consp/lcd8-re/src/hal/lcd8h/at32f435/cntl.c

#include "controls.h"
#include "comm.h"
#include "delay.h"
#include "lcd.h"
#include "at32f435_437.h"
#include "hal/lcd8/at32f435/cntl.h"

#include "config.h"
#include "eeprom.h"
#include "gui.h"

extern settings_t settings;

const int NTC_table[1025] = {
  105972, 90128, 74284, 66383, 61277, 57570, 
  54690, 52352, 50395, 48718, 47256, 45963, 
  44806, 43760, 42808, 41936, 41131, 40384, 
  39689, 39038, 38428, 37853, 37310, 36795, 
  36307, 35842, 35399, 34976, 34571, 34182, 
  33810, 33451, 33106, 32774, 32453, 32143, 
  31843, 31553, 31272, 30999, 30734, 30477, 
  30228, 29985, 29748, 29518, 29294, 29075, 
  28861, 28653, 28449, 28250, 28056, 27865, 
  27679, 27497, 27319, 27144, 26972, 26804, 
  26639, 26478, 26319, 26163, 26010, 25860, 
  25712, 25567, 25424, 25283, 25145, 25009, 
  24875, 24744, 24614, 24486, 24360, 24236, 
  24114, 23993, 23875, 23757, 23642, 23528, 
  23415, 23304, 23195, 23087, 22980, 22874, 
  22770, 22667, 22566, 22465, 22366, 22268, 
  22171, 22075, 21980, 21887, 21794, 21702, 
  21611, 21522, 21433, 21345, 21258, 21172, 
  21087, 21002, 20919, 20836, 20754, 20673, 
  20593, 20513, 20434, 20356, 20279, 20202, 
  20126, 20051, 19976, 19902, 19828, 19756, 
  19683, 19612, 19541, 19471, 19401, 19331, 
  19263, 19195, 19127, 19060, 18993, 18927, 
  18862, 18797, 18732, 18668, 18605, 18541, 
  18479, 18416, 18355, 18293, 18232, 18172, 
  18112, 18052, 17993, 17934, 17876, 17818, 
  17760, 17703, 17646, 17589, 17533, 17477, 
  17421, 17366, 17311, 17257, 17203, 17149, 
  17096, 17042, 16990, 16937, 16885, 16833, 
  16781, 16730, 16679, 16628, 16578, 16527, 
  16478, 16428, 16379, 16329, 16281, 16232, 
  16184, 16136, 16088, 16040, 15993, 15946, 
  15899, 15853, 15806, 15760, 15714, 15669, 
  15623, 15578, 15533, 15488, 15444, 15399, 
  15355, 15311, 15268, 15224, 15181, 15138, 
  15095, 15052, 15009, 14967, 14925, 14883, 
  14841, 14800, 14758, 14717, 14676, 14635, 
  14594, 14554, 14513, 14473, 14433, 14393, 
  14354, 14314, 14275, 14235, 14196, 14157, 
  14119, 14080, 14041, 14003, 13965, 13927, 
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
};
 
extern adc_data_t adc;
extern volatile uint32_t timer_counter;

extern uint8_t power_button_state ;
extern uint8_t up_button_state ;
extern uint8_t down_button_state ;
extern uint8_t nc_button_state ;
extern uint8_t light_state ;

extern uint32_t power_button_start;
extern uint32_t up_button_start;
extern uint32_t down_button_start;
extern uint32_t nc_button_start;
extern uint32_t button_backoff, button_backoff_start;

int32_t ext_temp_store = 0; // store temperature adc value in case button is pressed

/**
 * static functions
 */
static void adc_config(void) {
    adc_base_config_type adc_base_struct;
    crm_periph_clock_enable(CRM_ADC1_PERIPH_CLOCK, TRUE); // use default perph clock
    /* crm_adc_clock_div_set(CRM_ADC_DIV_6); // */

    adc_common_config_type adc_common_struct;
    adc_common_default_para_init(&adc_common_struct);
    adc_common_struct.combine_mode = ADC_INDEPENDENT_MODE;
    adc_common_struct.div = ADC_HCLK_DIV_4;
    adc_common_struct.common_dma_mode = ADC_COMMON_DMAMODE_DISABLE;
    adc_common_struct.common_dma_request_repeat_state = FALSE;
    adc_common_struct.sampling_interval = ADC_SAMPLING_INTERVAL_5CYCLES;
    adc_common_struct.tempervintrv_state = FALSE;
    adc_common_struct.vbat_state = FALSE;
    adc_common_config(&adc_common_struct);

    adc_base_default_para_init(&adc_base_struct);
    adc_base_struct.sequence_mode = TRUE;
    adc_base_struct.repeat_mode = FALSE;
    adc_base_struct.data_align = ADC_RIGHT_ALIGNMENT;
    adc_base_struct.ordinary_channel_length = 6;
    adc_base_config(ADC1, &adc_base_struct);
    adc_resolution_set(ADC1, ADC_RESOLUTION_12B);
    adc_ordinary_channel_set(ADC1, ADC_CHANNEL_16, 1, ADC_SAMPLETIME_247_5);
    adc_ordinary_channel_set(ADC1, ADC_CHANNEL_17, 2, ADC_SAMPLETIME_247_5);
    adc_ordinary_channel_set(ADC1, VOLTAGE_DETECT_ADC_CH, 3, ADC_SAMPLETIME_247_5);
    adc_ordinary_channel_set(ADC1, EXT_TEMP_ADC_CH, 4, ADC_SAMPLETIME_247_5);
    adc_ordinary_channel_set(ADC1, NC_BUTTON_ADC_CH, 5, ADC_SAMPLETIME_247_5);
    adc_ordinary_channel_set(ADC1, POWER_BUTTON_ADC_CH, 6, ADC_SAMPLETIME_247_5);

    adc_dma_request_repeat_enable(ADC1, TRUE);
    adc_ordinary_conversion_trigger_set(ADC1, ADC_ORDINARY_TRIG_TMR1CH1, ADC_ORDINARY_TRIG_EDGE_NONE);
    adc_ordinary_software_trigger_enable(ADC1, TRUE);
    /* adc_ordinary_conversion_trigger_set(ADC1, ADC123_ORDINARY_TRIG_SOFTWARE, TRUE); */

    adc_dma_mode_enable(ADC1, TRUE);
    /* adc_tempersensor_vintrv_enable(TRUE); // required only for temp sensor */

    adc_enable(ADC1, TRUE);
    adc_calibration_init(ADC1);
    while(adc_calibration_init_status_get(ADC1));
    adc_calibration_start(ADC1);
    while(adc_calibration_status_get(ADC1));
}

static void dma_config(void)
{
    dma_init_type dma_init_struct;
    crm_periph_clock_enable(CRM_DMA1_PERIPH_CLOCK, TRUE);
    dma_reset(DMA1_CHANNEL1);
    dma_default_para_init(&dma_init_struct);
    dma_init_struct.buffer_size = 6;
    dma_init_struct.direction = DMA_DIR_PERIPHERAL_TO_MEMORY;
    dma_init_struct.memory_base_addr = (uint32_t) &adc;
    dma_init_struct.memory_data_width = DMA_MEMORY_DATA_WIDTH_HALFWORD;
    dma_init_struct.memory_inc_enable = TRUE;
    dma_init_struct.peripheral_base_addr = (uint32_t)&(ADC1->odt);
    dma_init_struct.peripheral_data_width = DMA_PERIPHERAL_DATA_WIDTH_HALFWORD;
    dma_init_struct.peripheral_inc_enable = FALSE;
    dma_init_struct.priority = DMA_PRIORITY_HIGH;
    dma_init_struct.loop_mode_enable = TRUE;
    dma_init(DMA1_CHANNEL1, &dma_init_struct);

    dmamux_enable(DMA1, TRUE);
    dmamux_init(DMA1MUX_CHANNEL1, DMAMUX_DMAREQ_ID_ADC1);

    dma_channel_enable(DMA1_CHANNEL1, TRUE);
}

static void tmr_config(void) {

    crm_periph_clock_enable(CRM_TMR14_PERIPH_CLOCK, TRUE);
    /* tmr_output_config_type tmr_oc_init_structure; */
    /* tmre base configuration */
    tmr_base_init(TMR14,  BUTTON_MEASURE_PERIOD * 1000, TIMER_FREQ(1000000));
    /* tmr_base_init(TMR14,  BUTTON_MEASURE_PERIOD * 1000, 1000000); */
    tmr_cnt_dir_set(TMR14, TMR_COUNT_UP);
    tmr_clock_source_div_set(TMR14, TMR_CLOCK_DIV1);

    /* output compare toggle mode configuration: channel1 */
    /* tmr_output_default_para_init(&tmr_oc_init_structure); */
    /* tmr_oc_init_structure.oc_mode = TMR_OUTPUT_CONTROL_SWITCH; */
    /* tmr_oc_init_structure.oc_idle_state = FALSE; */
    /* tmr_oc_init_structure.oc_polarity = TMR_OUTPUT_ACTIVE_LOW; */
    /* tmr_oc_init_structure.oc_output_state = FALSE; */
    /* tmr_output_channel_config(TMR14, TMR_SELECT_CHANNEL_1, &tmr_oc_init_structure); */
    /* tmr_channel_value_set(TMR14, TMR_SELECT_CHANNEL_1, 1000); */
    tmr_counter_enable(TMR14, TRUE);
    tmr_interrupt_enable(TMR14, TMR_OVF_INT, TRUE);
    
    nvic_priority_group_config(NVIC_PRIORITY_GROUP_4);
    nvic_irq_enable(TMR8_TRG_HALL_TMR14_IRQn, 0, 0);
}

/**
 * public functions
 */

void controls_init(void) {
    // enable clocks
    crm_periph_clock_enable(CRM_GPIOA_PERIPH_CLOCK, TRUE);
    // configure pins
    //
    gpio_init_type gpio_initstructure;

    gpio_initstructure.gpio_out_type       = GPIO_OUTPUT_PUSH_PULL; // input
    gpio_initstructure.gpio_pull           = POWER_BUTTON_PULL; // external pullup
    gpio_initstructure.gpio_mode           = POWER_BUTTON_MODE;
    gpio_initstructure.gpio_drive_strength = GPIO_DRIVE_STRENGTH_STRONGER; // input
    gpio_initstructure.gpio_pins           = POWER_BUTTON_PIN;
    gpio_init(POWER_BUTTON_GPIO, &gpio_initstructure);

    gpio_initstructure.gpio_out_type       = GPIO_OUTPUT_PUSH_PULL; // input
    gpio_initstructure.gpio_pull           = UP_BUTTON_PULL; // external pullup
    gpio_initstructure.gpio_mode           = UP_BUTTON_MODE;
    gpio_initstructure.gpio_drive_strength = GPIO_DRIVE_STRENGTH_STRONGER; // input
    gpio_initstructure.gpio_pins           = UP_BUTTON_PIN;
    gpio_init(UP_BUTTON_GPIO, &gpio_initstructure);

    gpio_initstructure.gpio_out_type       = GPIO_OUTPUT_PUSH_PULL; // input
    gpio_initstructure.gpio_pull           = DOWN_BUTTON_PULL; // external pullup
    gpio_initstructure.gpio_mode           = DOWN_BUTTON_MODE;
    gpio_initstructure.gpio_drive_strength = GPIO_DRIVE_STRENGTH_STRONGER; // input
    gpio_initstructure.gpio_pins           = DOWN_BUTTON_PIN;
    gpio_init(DOWN_BUTTON_GPIO, &gpio_initstructure);

    gpio_initstructure.gpio_out_type       = GPIO_OUTPUT_PUSH_PULL; // input
    gpio_initstructure.gpio_pull           = POWER_LATCH_PULL; // external pullup
    gpio_initstructure.gpio_mode           = POWER_LATCH_MODE;
    gpio_initstructure.gpio_drive_strength = GPIO_DRIVE_STRENGTH_STRONGER; // input
    gpio_initstructure.gpio_pins           = POWER_LATCH_PIN;
    gpio_init(POWER_LATCH_GPIO, &gpio_initstructure);

    gpio_initstructure.gpio_out_type       = GPIO_OUTPUT_PUSH_PULL; // input
    gpio_initstructure.gpio_pull           = VOLTAGE_DETECT_PULL; // external pullup
    gpio_initstructure.gpio_mode           = VOLTAGE_DETECT_MODE;
    gpio_initstructure.gpio_drive_strength = GPIO_DRIVE_STRENGTH_STRONGER; // input
    gpio_initstructure.gpio_pins           = VOLTAGE_DETECT_PIN;
    gpio_init(VOLTAGE_DETECT_GPIO, &gpio_initstructure);

    gpio_initstructure.gpio_out_type       = GPIO_OUTPUT_PUSH_PULL; // input
    gpio_initstructure.gpio_pull           = NC_BUTTON_PULL; // external pullup
    gpio_initstructure.gpio_mode           = NC_BUTTON_MODE;
    gpio_initstructure.gpio_drive_strength = GPIO_DRIVE_STRENGTH_STRONGER; // input
    gpio_initstructure.gpio_pins           = NC_BUTTON_PIN;
    gpio_init(NC_BUTTON_GPIO, &gpio_initstructure);

#ifdef LEXT_INSTALLED
    /* gpio_initstructure.gpio_out_type       = GPIO_OUTPUT_PUSH_PULL; // input */
    /* gpio_initstructure.gpio_pull           = GPIO_PULL_NONE; // external pullup */
    /* gpio_initstructure.gpio_mode           = GPIO_MODE_MUX; */
    /* gpio_initstructure.gpio_drive_strength = GPIO_DRIVE_STRENGTH_STRONGER; // input */
    /* gpio_initstructure.gpio_pins           = GPIO_PINS_3; */
    /* gpio_init(VOLTAGE_DETECT_GPIO, &gpio_initstructure); */
#endif

    // configure ADC
    //
    dma_config();
    adc_config();
    tmr_config();

}

CRITICAL void power_enable(void) { POWER_LATCH_GPIO->scr = POWER_LATCH_PIN; }
CRITICAL void power_disable(void) { 
    lcd_backlight(0); // "show off"
#if UART_COMM == UART_COMM_VESC
    comm_vesc_packet_send_shutdown();
#endif
    int n = 0;
    while(n < 100) {
#ifndef DEBUG
        wdt_counter_reload();
#endif
        delay_ms(25);
        n++;
    }
    // cap should keep it fed for a while
    POWER_LATCH_GPIO->clr = POWER_LATCH_PIN; 
#if LEXT_INSTALLED
    // keep alive on batt power
    // if not backup batt installed brownout will happen
    /* EXINT->inten |= EXINT_LINE_6; */
    /* pwc_voltage_regulate_set(PWC_REGULATOR_LOW_POWER); // does almost nothing */
    /* pwc_deep_sleep_mode_enter(PWC_DEEP_SLEEP_ENTER_WFI);  */
    // goes to deepsleep, power consumption in deepsleep and standby is the same (mostly leakage anyway)
    // recover on interrupt

    /* wait clock stable */
    /* for(int index = 0; index < 300; index++) */
    /* { */
    /*   __NOP(); */
    /* } */
    /* pwc_voltage_regulate_set(PWC_REGULATOR_ON); */
    /*  */
    /* // reset */
    /* NVIC_SystemReset(); */
#endif
}

volatile uint32_t xun = 0;
static inline int power_button_measure(void) {
    if (POWER_BUTTON_MODE == GPIO_MODE_INPUT) return (POWER_BUTTON_GPIO->idt & (POWER_BUTTON_PIN)) > 0;
    return adc.power_button >= 3*1024;
}

static inline int down_button_measure(void) {
    if (DOWN_BUTTON_MODE == GPIO_MODE_INPUT) return (DOWN_BUTTON_GPIO->idt & (DOWN_BUTTON_PIN)) == 0;
    return adc.down_button <= 10;
}

static inline int up_button_measure(void) {
    if (UP_BUTTON_MODE == GPIO_MODE_INPUT) return (UP_BUTTON_GPIO->idt & (UP_BUTTON_PIN)) == 0;
    return adc.up_button <= 10;
}

static inline int nc_button_measure(void) {
    if (NC_BUTTON_MODE == GPIO_MODE_INPUT) return (NC_BUTTON_GPIO->idt & (NC_BUTTON_PIN)) > 0;
    return adc.nc_button <= 10;
}

int32_t int_temp(void) {
    // data from artery example code converted to return 24.8s fixed point format
#define ADC_TEMP_BASE                    ((int32_t)(1638))
#define ADC_TEMP_SLOPE                   ((int32_t)(-4551))
    return (((ADC_TEMP_BASE - adc.temperature_int) << 16) / ADC_TEMP_SLOPE) + (25 << 8);
}

int32_t ext_temp(void) {
    // result is in 24.8s format
    // value is stored for when button is pressed as it pulls to ground
    if (adc.temperature_ext <= 10) {
        return ext_temp_store;
    } else {
        return ext_temp_store = NTC_ADC2Temperature(adc.temperature_ext);
    }
}

int32_t light_level(void) {
    return adc.nc_button;
}

void auto_lights() {
    if (settings.lights_mode == LIGHTS_MODE_AUTOMATIC) {
        if (light_level() > settings.light_sensitivity && !settings.lights_enabled) {
            settings.lights_enabled = 1;
            draw_lights_trigger = 1;
            comm_send_display_status();
        } else if (light_level() < settings.light_sensitivity && settings.lights_enabled) {
            settings.lights_enabled = 0;
            draw_lights_trigger = 1;
            comm_send_display_status();
        }
    }
}

static inline void measure_buttons(void) {
    // trigger adc
    adc_ordinary_software_trigger_enable(ADC1, TRUE);
    // button press addition
    if (timer_counter < button_backoff + button_backoff_start) return;
    if (up_button_measure()) {
        if (up_button_state == BUTTON_RELEASED) {
            up_button_start = timer_counter;
            up_button_state = BUTTON_DOWN;
        } else if (up_button_state == BUTTON_DOWN && timer_counter - up_button_start > BUTTON_LONG_PRESS_TIME) {
            up_button_state = BUTTON_LONG_PRESSED;
        }
    } else {
        if (up_button_state == BUTTON_DOWN && timer_counter - up_button_start > BUTTON_DEBOUNCE_TIME) {
            up_button_state = up_button_state == BUTTON_DOWN ? BUTTON_PRESSED : BUTTON_RELEASED;
            up_button_start = 0;
        } else if (up_button_state != BUTTON_PRESSED) {
            up_button_state = BUTTON_RELEASED;
            up_button_start = 0;
        }
    }

    if (down_button_measure()) {
        if (down_button_state == BUTTON_RELEASED) {
            down_button_start = timer_counter;
            down_button_state = BUTTON_DOWN;
        } else if (down_button_state == BUTTON_DOWN && timer_counter - down_button_start > BUTTON_LONG_PRESS_TIME) {
            down_button_state = BUTTON_LONG_PRESSED;
        }
    } else {
        if (down_button_state == BUTTON_DOWN && timer_counter - down_button_start > BUTTON_DEBOUNCE_TIME) {
            down_button_state = down_button_state == BUTTON_DOWN ? BUTTON_PRESSED : BUTTON_RELEASED;
            down_button_start = 0;
        } else if (down_button_state != BUTTON_PRESSED) {
            down_button_state = BUTTON_RELEASED;
            down_button_start = 0;
        }
    }

    if (power_button_measure()) {
        if (power_button_state == BUTTON_RELEASED) {
            power_button_start = timer_counter;
            power_button_state = BUTTON_DOWN;
        } else if (power_button_state == BUTTON_DOWN && timer_counter - power_button_start > BUTTON_LONG_PRESS_TIME) {
            power_button_state = BUTTON_LONG_PRESSED;
        }
    } else {
        if (power_button_state == BUTTON_DOWN && timer_counter - power_button_start > BUTTON_DEBOUNCE_TIME) {
            power_button_state = power_button_state == BUTTON_DOWN ? BUTTON_PRESSED : BUTTON_RELEASED;
            power_button_start = 0;
        } else if (power_button_state != BUTTON_PRESSED) {
            power_button_state = BUTTON_RELEASED;
            power_button_start = 0;
        }
    }
    if (nc_button_measure()) {
        if (nc_button_state == BUTTON_RELEASED) {
            nc_button_start = timer_counter;
            nc_button_state = BUTTON_DOWN;
        } else if (timer_counter - nc_button_start > BUTTON_LONG_PRESS_TIME) {
            nc_button_state = BUTTON_LONG_PRESSED;
        }
    } else {
        if (nc_button_state == BUTTON_DOWN && timer_counter - nc_button_start > BUTTON_DEBOUNCE_TIME) {
            nc_button_state = nc_button_state == BUTTON_DOWN ? BUTTON_PRESSED : BUTTON_RELEASED;
            nc_button_start = 0;
        } else if (nc_button_state != BUTTON_PRESSED) {
            nc_button_state = BUTTON_RELEASED;
            nc_button_start = 0;
        }
    }
}


CRITICAL void TMR8_TRG_HALL_TMR14_IRQHandler(void)
{
    if(tmr_interrupt_flag_get(TMR14, TMR_OVF_FLAG) != RESET)
    {
        tmr_flag_clear(TMR14, TMR_OVF_FLAG );
        measure_buttons();
    }
}

/**
* The NTC table has 1025 interpolation points.
* Unit:0.00390625 °C (results in 8.8 format)
* All credits: https://www.sebulli.com/ntc/index.php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
*
*/
 
 
/**
* \brief    Converts the ADC result into a temperature value.
*
*           P1 and p2 are the interpolating point just before and after the
*           ADC value. The function interpolates between these two points
*           The resulting code is very small and fast.
*           Only one integer multiplication is used.
*           The compiler can replace the division by a shift operation.
*
*           In the temperature range from -20°C to 70°C the error
*           caused by the usage of a table is 0.005°C
*
* \param    adc_value  The converted ADC result
* \return              The temperature in 0.00390625 °C
*
*/ 
int32_t NTC_ADC2Temperature(int16_t adc_value) {
 
  int p1,p2;
  /* Estimate the interpolating point before and after the ADC value. */
  p1 = NTC_table[ (adc_value >> 2)  ];
  p2 = NTC_table[ (adc_value >> 2)+1];
 
  /* Interpolate between both points. */
  return p1 - ( (p1-p2) * (adc_value & 0x0003) ) / 4;
};

int32_t voltage_mcu(void) {
    return 0;
}

int32_t voltage_ebat(void) { // in mv
    return (adc.voltage_battery << 16) / 2598;//10150; // 24.8
}
