consp/lcd8-re/src/hal/lcd8h/at32f435/sysclock.c

/**
  **************************************************************************
  * @file     at32f415_clock.c
  * @brief    system clock config program
  **************************************************************************
  *                       Copyright notice & Disclaimer
  *
  * The software Board Support Package (BSP) that is made available to
  * download from Artery official website is the copyrighted work of Artery.
  * Artery authorizes customers to use, copy, and distribute the BSP
  * software and its related documentation for the purpose of design and
  * development in conjunction with Artery microcontrollers. Use of the
  * software is governed by this copyright notice and the following disclaimer.
  *
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
  **************************************************************************
  */

/* includes ------------------------------------------------------------------*/
#include "at32f435_437.h"
#include "delay.h"
#include "config.h"

/**
  * @brief  config sclk 144 mhz with hick clock source.
  * @note   the system clock is configured as follow:
  *         system clock (sclk)   = hick / 2 * pll_mult
  *         system clock source   = pll (hick)
  *         - hick                = HICK_VALUE
  *         - sclk                = 144000000
  *         - ahbdiv              = 1
  *         - ahbclk              = 144000000
  *         - apb2div             = 2
  *         - apb2clk             = 72000000
  *         - apb1div             = 2
  *         - apb1clk             = 72000000
  *         - pll_mult            = 36
  *         - flash_wtcyc         = 4 cycle
  * @param  none
  * @retval none
  */

extern uint32_t reset_flag;
CRITICAL void system_clock_config(void)
{
/* reset crm */
  crm_reset();

  /* enable pwc periph clock */
  crm_periph_clock_enable(CRM_PWC_PERIPH_CLOCK, TRUE);

  /* config ldo voltage */
  pwc_ldo_output_voltage_set(PWC_LDO_OUTPUT_1V3);
 
  /* set the flash clock divider */
  flash_clock_divider_set(CONF_FLASH_DIV);

  /* enable hext */
  crm_clock_source_enable(CLOCK_SOURCE, TRUE);

   /* wait till hext is ready */
  while(crm_hext_stable_wait() == ERROR)
  {
  }

  /* config pll clock resource
  common frequency config list: pll source selected  hick or hext(8mhz)
  _________________________________________________________________________________________________
  |        |         |         |         |         |         |         |         |        |        |
  |pll(mhz)|   288   |   252   |   216   |   192   |   180   |   144   |   108   |   72   |   36   |
  |________|_________|_________|_________|_________|_________|_________|_________|_________________|
  |        |         |         |         |         |         |         |         |        |        |
  |pll_ns  |   144   |   126   |   108   |   96    |   90    |   72    |   108   |   72   |   72   |
  |        |         |         |         |         |         |         |         |        |        |
  |pll_ms  |   1     |   1     |   1     |   1     |   1     |   1     |   1     |   1    |   1    |
  |        |         |         |         |         |         |         |         |        |        |
  |pll_fr  |   FR_4  |   FR_4  |   FR_4  |   FR_4  |   FR_4  |   FR_4  |   FR_8  |   FR_8 |   FR_16|
  |________|_________|_________|_________|_________|_________|_________|_________|________|________|

  if pll clock source selects hext with other frequency values, or configure pll to other
  frequency values, please use the at32 new clock  configuration tool for configuration.  */
  crm_pll_config(PLL_SOURCE, CONF_PLL_MUL, CONF_PLL_PREDIV, CONF_PLL_POSTDIV);

  /* enable pll */
  crm_clock_source_enable(CRM_CLOCK_SOURCE_PLL, TRUE);

  /* wait till pll is ready */
  while(crm_flag_get(CRM_PLL_STABLE_FLAG) != SET)
  {
  }

  /* config ahbclk */
  crm_ahb_div_set(CRM_AHB_DIV_1);

  /* config apb2clk */
  crm_apb2_div_set(CRM_APB2_DIV_2);

  /* config apb1clk */
  crm_apb1_div_set(CRM_APB1_DIV_2);

  /* enable auto step mode */
  crm_auto_step_mode_enable(TRUE);

  /* select pll as system clock source */
  crm_sysclk_switch(CRM_SCLK_PLL);

  /* wait till pll is used as system clock source */
  while(crm_sysclk_switch_status_get() != CRM_SCLK_PLL)
  {
  }

  /* disable auto step mode */
  crm_auto_step_mode_enable(FALSE);

  /* update system_core_clock global variable */
  system_core_clock_update();

}

/* unlock >128k */
CRITICAL void extend_sram(void)
{
  /* check if ram has been set to expectant size, if not, change eopb0 */
  if (((USD->eopb0) & 0x07) != FLASH_EOPB0_SRAM_384K)
  {
    flash_unlock();
    /* erase user system data bytes */
    flash_user_system_data_erase();
    /* change sram size */
    flash_eopb0_config(FLASH_EOPB0_SRAM_384K);
    /* system reset */
    nvic_system_reset();
  }
}
