consp/lcd8-re/src/hal/lcd8h/at32f435/at32f435_437_int.c

/**
  **************************************************************************
  * @file     at32f435_437_int.c
  * @brief    main interrupt service routines.
  **************************************************************************
  *                       Copyright notice & Disclaimer
  *
  * The software Board Support Package (BSP) that is made available to
  * download from Artery official website is the copyrighted work of Artery.
  * Artery authorizes customers to use, copy, and distribute the BSP
  * software and its related documentation for the purpose of design and
  * development in conjunction with Artery microcontrollers. Use of the
  * software is governed by this copyright notice and the following disclaimer.
  *
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
  **************************************************************************
  */

/* includes ------------------------------------------------------------------*/
#include "at32f435_437_int.h"
#include "config.h"

/** @addtogroup AT32F435_periph_template
  * @{
  */

/** @addtogroup 435_LED_toggle
  * @{
  */

/**
  * @brief  this function handles nmi exception.
  * @param  none
  * @retval none
  */
CRITICAL void NMI_Handler(void)
{
    while(1);
}

/**
  * @brief  this function handles hard fault exception.
  * @param  none
  * @retval none
  */
CRITICAL void HardFault_Handler(void)
{
  /* go to infinite loop when hard fault exception occurs */
  while(1)
  {
  }
}

/**
  * @brief  this function handles memory manage exception.
  * @param  none
  * @retval none
  */
CRITICAL void MemManage_Handler(void)
{
  /* go to infinite loop when memory manage exception occurs */
  while(1)
  {
  }
}

/**
  * @brief  this function handles bus fault exception.
  * @param  none
  * @retval none
  */
CRITICAL void BusFault_Handler(void)
{
  /* go to infinite loop when bus fault exception occurs */
  while(1)
  {
  }
}

/**
  * @brief  this function handles usage fault exception.
  * @param  none
  * @retval none
  */
CRITICAL void UsageFault_Handler(void)
{
  /* go to infinite loop when usage fault exception occurs */
  while(1)
  {
  }
}

/**
  * @brief  this function handles svcall exception.
  * @param  none
  * @retval none
  */
CRITICAL void SVC_Handler(void)
{
    asm("subs PC, LR, 0");
}

/**
  * @brief  this function handles debug monitor exception.
  * @param  none
  * @retval none
  */
CRITICAL void DebugMon_Handler(void)
{
    while(1);
}

/**
  * @brief  this function handles pendsv_handler exception.
  * @param  none
  * @retval none
  */
CRITICAL void PendSV_Handler(void)
{
    while(1);
}

/**
  * @brief  this function handles systick handler.
  * @param  none
  * @retval none
  */
CRITICAL void SysTick_Handler(void)
{
    while(1);
}

/**
  * @}
  */

/**
  * @}
  */
