consp/lcd8-re/inc/ugui/ugui_fonts.h

#ifndef __UGUI_FONTS_DATA_H
#define __UGUI_FONTS_DATA_H

/* -------------------------------------------------------------------------------- */
/* -- µGUI FONTS                                                                 -- */
/* -- Source: http://www.mikrocontroller.net/user/show/benedikt                  -- */
/* -------------------------------------------------------------------------------- */
#include "ugui.h"
/*
  Old fonts converted to new structure. They use Code Page 850 encoding. UTF-8 can be disabled if only these fonts are being used.
  https://en.wikipedia.org/wiki/Code_page_850
*/

#ifdef UGUI_USE_FONT_ANDALEMO_4X7
extern UG_FONT FONT_ANDALEMO_4X7[];
#endif
#ifdef UGUI_USE_FONT_ANDALEMO_5X8
extern UG_FONT FONT_ANDALEMO_5X8[];
#endif
#ifdef UGUI_USE_FONT_ANDALEMO_46X71
extern UG_FONT FONT_ANDALEMO_46X71[];
#endif
#ifdef UGUI_USE_FONT_ANDALEMO_6X9_MONO
extern UG_FONT FONT_ANDALEMO_6X9_MONO[];
#endif
#ifdef UGUI_USE_FONT_ANDALEMO_6X10_MONO
extern UG_FONT FONT_ANDALEMO_6X10_MONO[];
#endif
#ifdef UGUI_USE_FONT_ANDALEMO_12X20
extern UG_FONT FONT_ANDALEMO_12X20[];
#endif
#ifdef UGUI_USE_FONT_ANDALEMO_12X19
extern UG_FONT FONT_ANDALEMO_12X19[];
#endif
#ifdef UGUI_USE_FONT_ANDALEMO_12X18
extern UG_FONT FONT_ANDALEMO_12X18[];
#endif
#ifdef UGUI_USE_FONT_ANDALEMO_16X24
extern UG_FONT FONT_ANDALEMO_16X24[];
#endif
#ifdef UGUI_USE_FONT_ANDALEMO_93X143
extern UG_FONT FONT_ANDALEMO_93X143[];
#endif

#ifdef UGUI_USE_FONT_4X6
extern UG_FONT FONT_4X6[];
#endif

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
#ifdef UGUI_USE_FONT_arial_45X52_CYRILLIC
extern UG_FONT FONT_arial_45X52_CYRILLIC[];
#endif
#ifdef UGUI_USE_FONT_arial_49X57
extern UG_FONT FONT_arial_49X57[];
#endif
#ifdef UGUI_USE_FONT_arial_49X57_CYRILLIC
extern UG_FONT FONT_arial_49X57_CYRILLIC[];
#endif

#endif // __UGUI_FONTS_DATA_H
