consp/lcd8-re/inc/uart.h

#ifndef __UART_H__
#define __UART_H__

#include <stdint.h>
#include <unistd.h>
#include "config.h"

// keep TX buffer at least as large as the largest message
// keep RX buffer at least as large as twice the largest received message
#ifdef DEBUG
#define UART_TX_BUFFER_SIZE     128
#define UART_RX_BUFFER_SIZE     128
#else
#define UART_TX_BUFFER_SIZE     64 
#define UART_RX_BUFFER_SIZE     128
#endif


void uart_init(uint32_t cnt_baud, uint32_t bt_baud);
void cnt_send(const uint8_t *buffer, ssize_t length);
void bt_send(const uint8_t *buffer, uint32_t length);
void bt_send_init(uint32_t program);
void bt_reset(void);
void bt_check(void);
void bt_send_battery(uint8_t level);
void bt_send_cmd(uint8_t id);
int uart_get_data(uint8_t *data, uint32_t *length);

// guard for tx buffer, not all gcc versions will detact overflows correctly
// and you might end up bashing some other memory region, MCCONF_TEMP uses 59 bytes
#if (UART_COMM == UART_COMM_VESC) && (UART_TX_BUFFER_SIZE < 64 || UART_RX_BUFFER_SIZE < 64)
#pragma error("Need at least 64 byte buffer for VESC")
#endif

#endif // __UART_H__
