consp/lcd8-re/inc/delay.h

#include <stdio.h>
#include <stdint.h>
#ifndef SIM
#else
#include <time.h>
#endif

#define NS_CALC(s) (s / 10)

void delay_init(void);
void delay_10ns(uint32_t ns);
void delay_us(uint32_t nus);
void delay_ms(uint16_t nms);
void delay_sec(uint16_t sec);
